Thinkpad4by3/chibitron/deflection_amp_5/deflection_amp_5/FOCUS_AMP.asc

C1: Cap; 100p
C2: Cap; 100p
Q1: npn
R1: Res; R=table(time,0,1000Meg,200ms,1000Meg,200.001ms,10Meg, 700ms,10Meg, 700.001ms, 1000Meg)
R2: Res; 5k
R3: Res; 5Meg
R4: Res; 10k
R5: Res; 100k
R6: Res; 100k
R12: Res; 3Meg
U2: LT1800
V1: Voltage; 10
V2: Voltage; PULSE(0 2 1p 40ms 40ms 20ms 0 10)
V4: Voltage; 2000
Named nets: 0, 5v, vout
.tran 1s
