Thinkpad4by3/chibitron/deflection_amp_5/deflection_amp_5/deflection_amp_3.kicad_sch

## KiCad design deflection_amp_5/deflection_amp_5/deflection_amp_3.kicad_sch (2026-02-02)

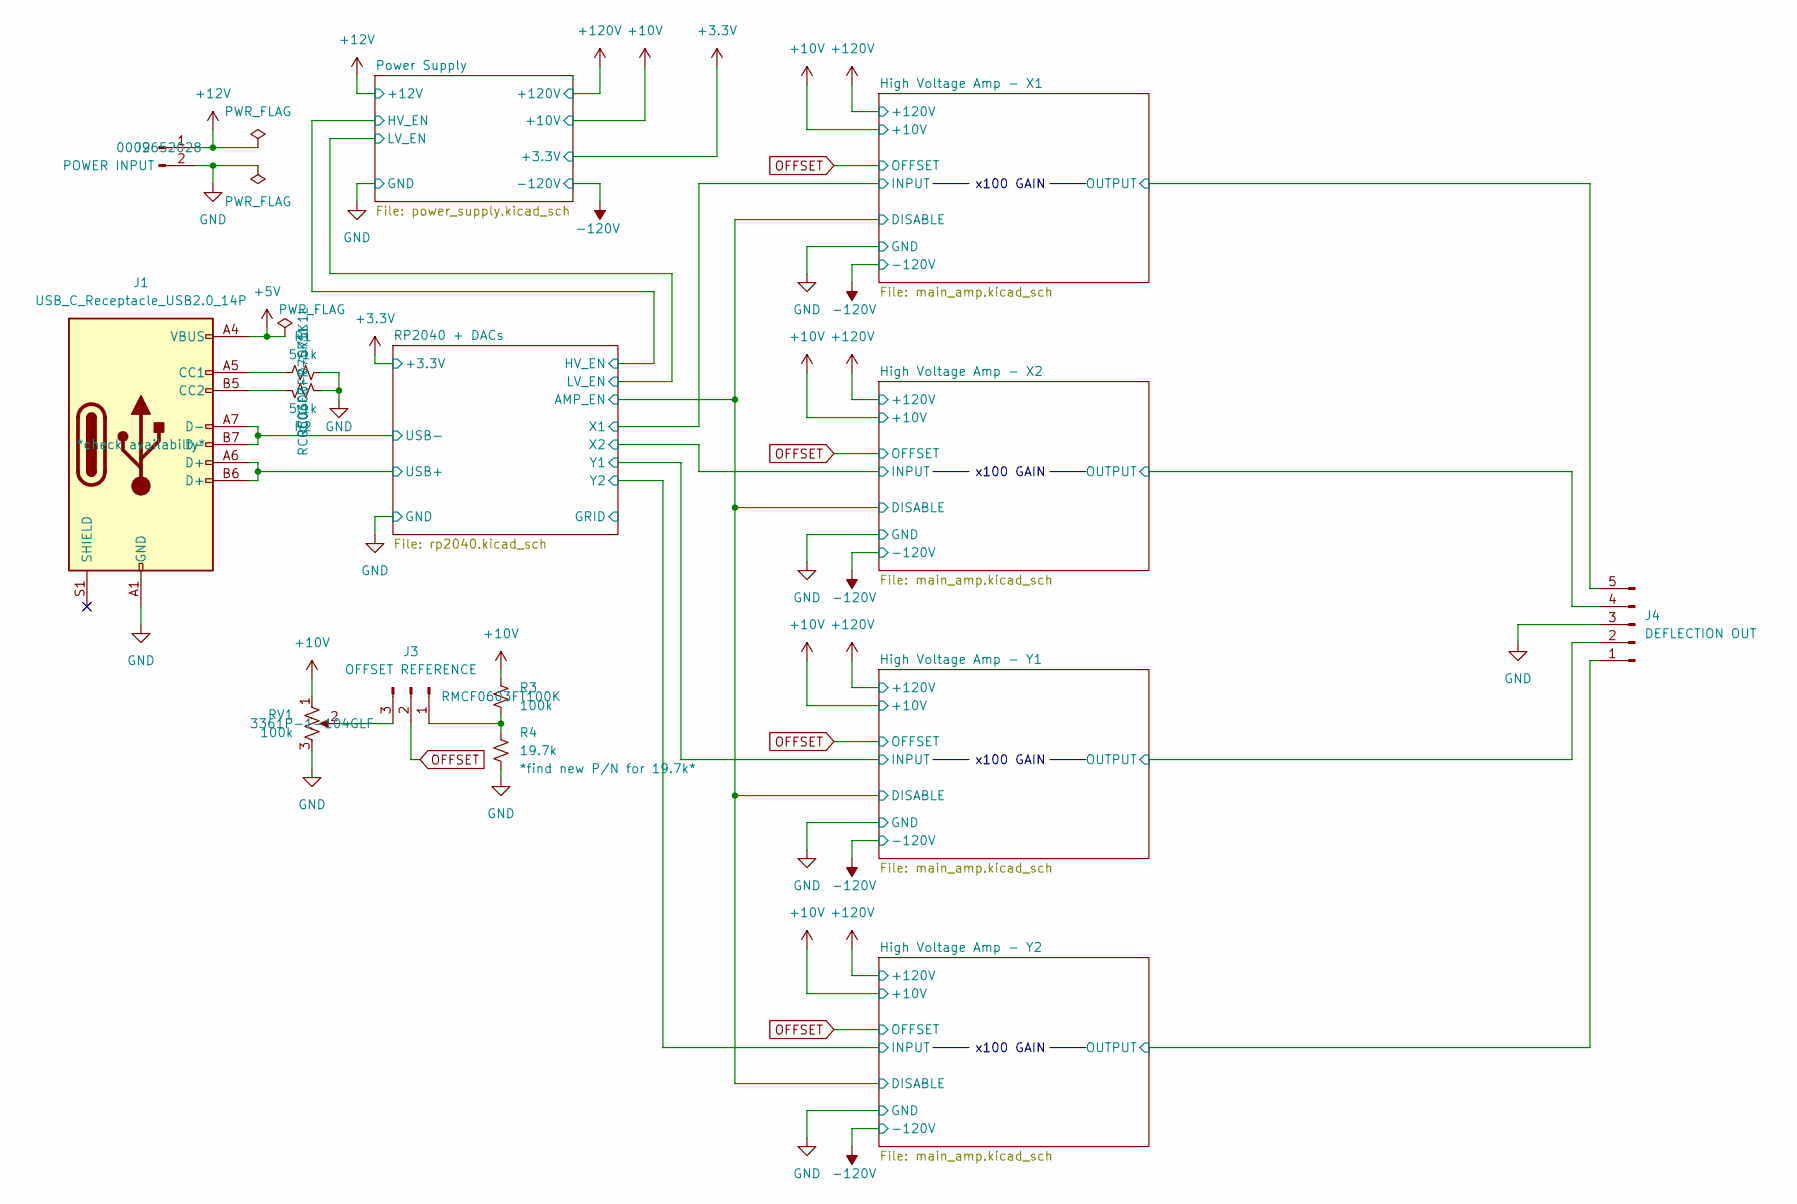
[picture p9: schematic deflection_amp_3.kicad_sch]

Parts:
J1: USB_C_Receptacle_USB2.0_14P; USB_C_Receptacle_HRO_TYPE-C-31-M-17; Digikey P/N *check availabilty*
J2: POWER INPUT; Molex_KK-396_5273-02A_1x02_P3.96mm_Vertical; Digikey P/N 0009652028
J3: OFFSET REFERENCE; PinSocket_1x03_P2.54mm_Vertical
J4: DEFLECTION OUT; Molex_KK-396_5273-05A_1x05_P3.96mm_Vertical
R1, R2: 5.1k; R_0603_1608Metric; Digikey P/N RC0603FR-075K1L
R3: 100k; R_0603_1608Metric; Digikey P/N RMCF0603FT100K
R4: 19.7k; R_0603_1608Metric; Digikey P/N *find new P/N for 19.7k*
RV1: 100k; Potentiometer_Vishay_TS53YJ_Vertical; Digikey P/N 3361P-1-104GLF

Connections:
+5V: J1.A4 (VBUS), J1.A9 (VBUS), J1.B4 (VBUS), J1.B9 (VBUS)
+10V: R3.1, RV1.1
+12V: J2.1
GND: J1.A1 (GND), J1.A12 (GND), J1.B1 (GND), J1.B12 (GND), J2.2, J4.3, R1.2, R2.2, R4.2, RV1.3
unnamed: J1.A5 (CC1), R1.1
unnamed: J1.B5 (CC2), R2.1
unnamed: J3.1, R3.2, R4.1
unnamed: J3.3, RV1.2
OFFSET: J3.2
OUTPUT: J4.1, J4.2, J4.4, J4.5
USB+: J1.A6 (D+), J1.B6 (D+)
USB-: J1.A7 (D-), J1.B7 (D-)

Notes on the sheet:
x100 GAIN
