Thinkpad4by3/chibitron/deflection_amp_5/deflection_amp_5/deflection_amp_5.kicad_sch

## KiCad design deflection_amp_5/deflection_amp_5/deflection_amp_5.kicad_sch (2026-02-02)

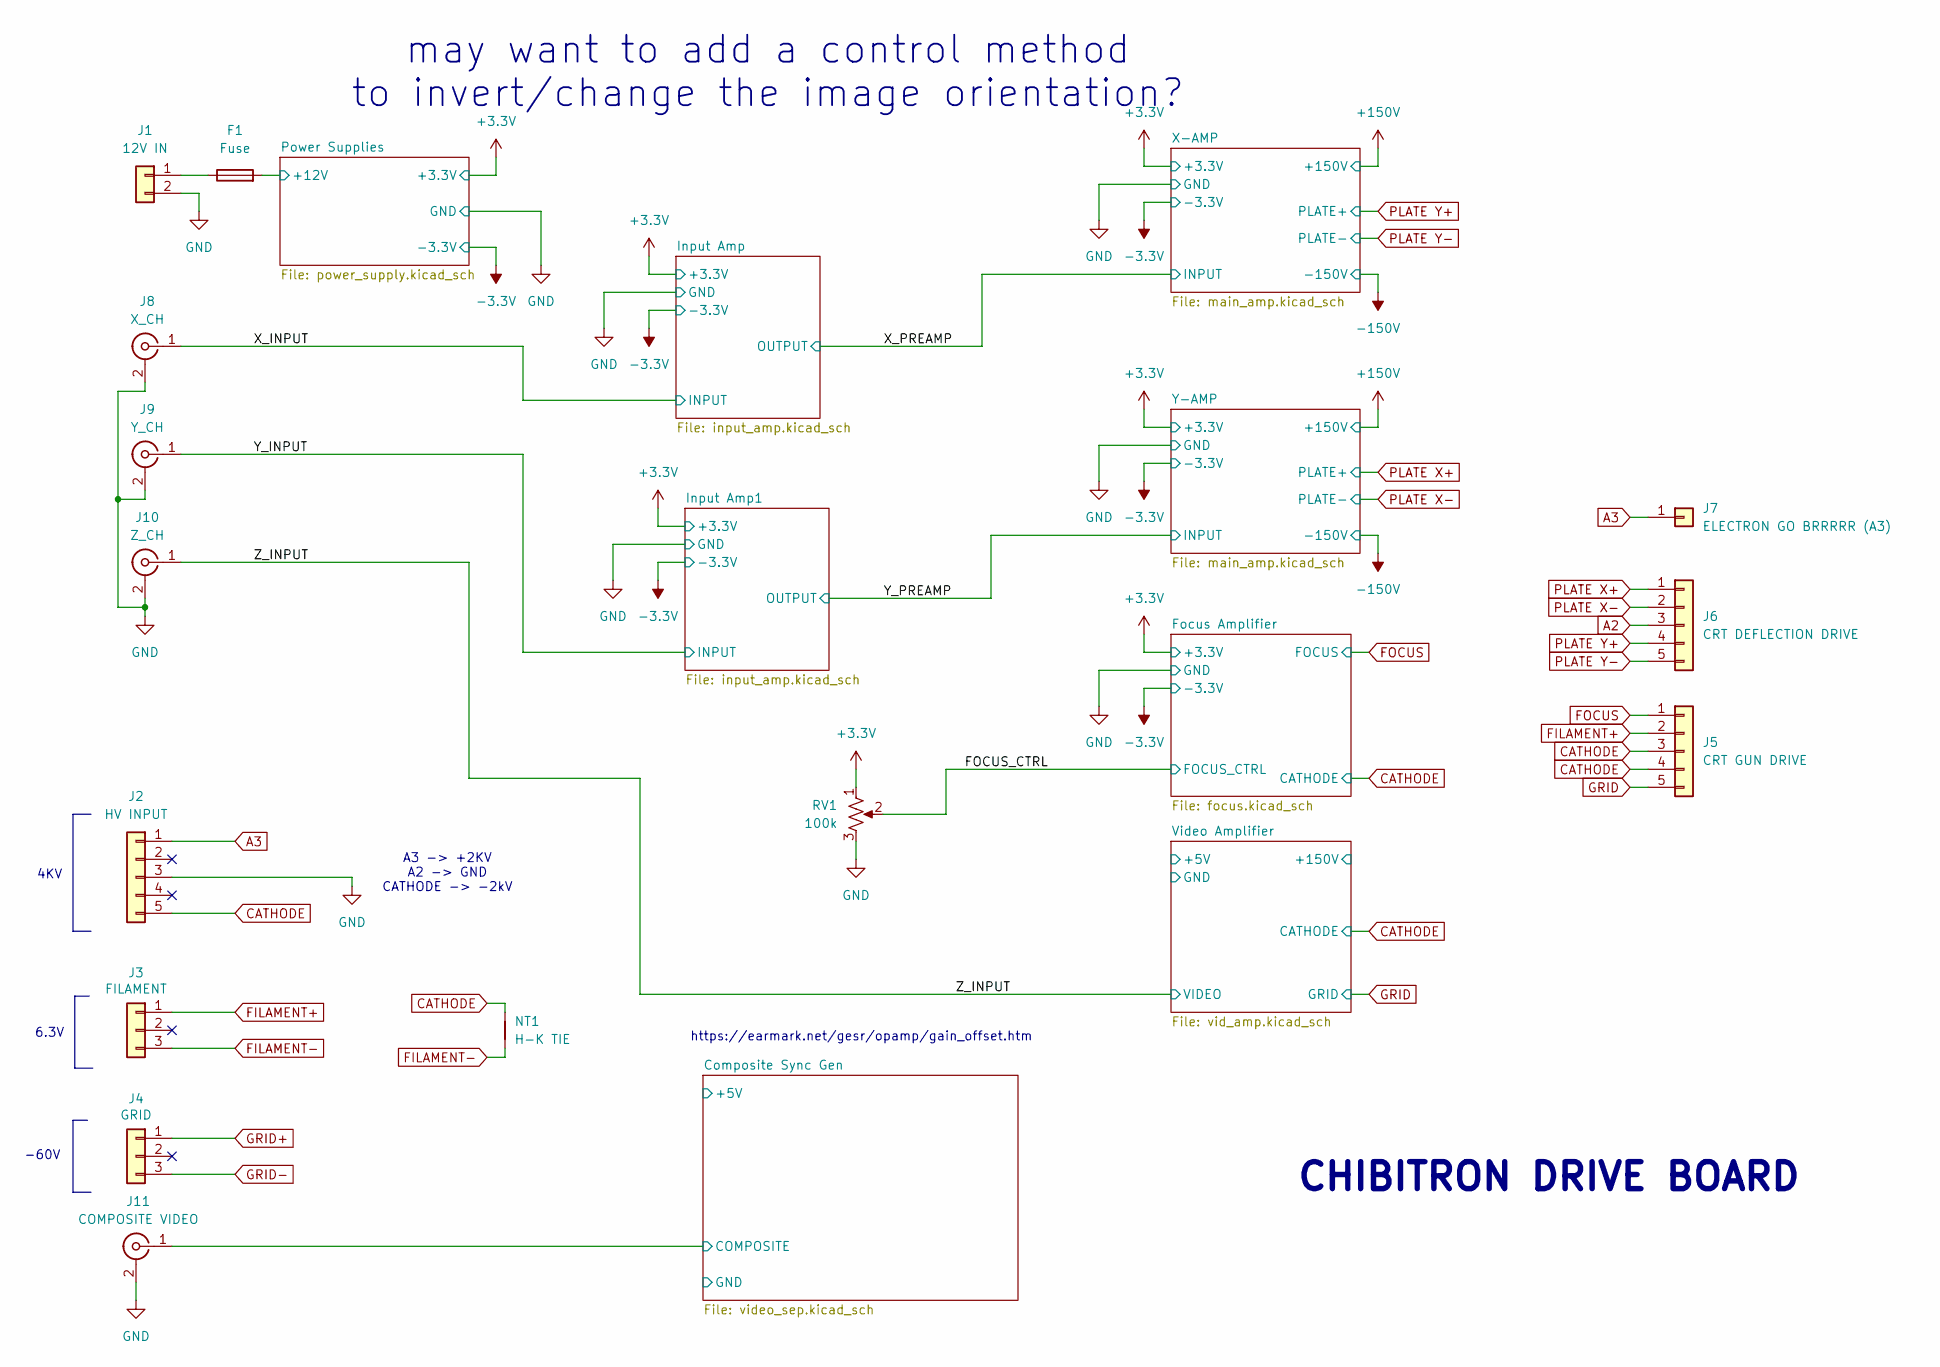
[picture p10: schematic deflection_amp_5.kicad_sch]

Parts:
F1: Fuse
J1: 12V IN
J2: HV INPUT
J3: FILAMENT
J4: GRID
J5: CRT GUN DRIVE
J6: CRT DEFLECTION DRIVE
J7: ELECTRON GO BRRRRR (A3)
J8: X_CH
J9: Y_CH
J10: Z_CH
J11: COMPOSITE VIDEO
NT1: H-K TIE
RV1: 100k

Connections:
+3.3V: RV1.1
+12V: F1.2
A2: J6.3
A3: J2.1, J7.1
CATHODE: J2.5, J5.3, J5.4, NT1.2
COMPOSITE: J11.1 (In)
FILAMENT+: J3.1, J5.2
FILAMENT-: J3.3, NT1.1
FOCUS: J5.1
FOCUS_CTRL: RV1.2
GND: J1.2, J2.3, J8.2 (Ext), J9.2 (Ext), J10.2 (Ext), J11.2 (Ext), RV1.3
GRID: J5.5
GRID+: J4.1
GRID-: J4.3
unnamed: F1.1, J1.1
PLATE X+: J6.1
PLATE X-: J6.2
PLATE Y+: J6.4
PLATE Y-: J6.5
X_INPUT: J8.1 (In)
Y_INPUT: J9.1 (In)
Z_INPUT: J10.1 (In)

Notes on the sheet:
A3 -> +2KV A2 -> GND CATHODE -> -2kV
CHIBITRON DRIVE BOARD
4KV
6.3V
https://earmark.net/gesr/opamp/gain_offset.htm
may want to add a control method to invert/change the image orientation?
-60V
