Thinkpad4by3/chibitron/deflection_amp_5/deflection_amp_5/focus.kicad_sch

## KiCad design deflection_amp_5/deflection_amp_5/focus.kicad_sch (2026-02-02)

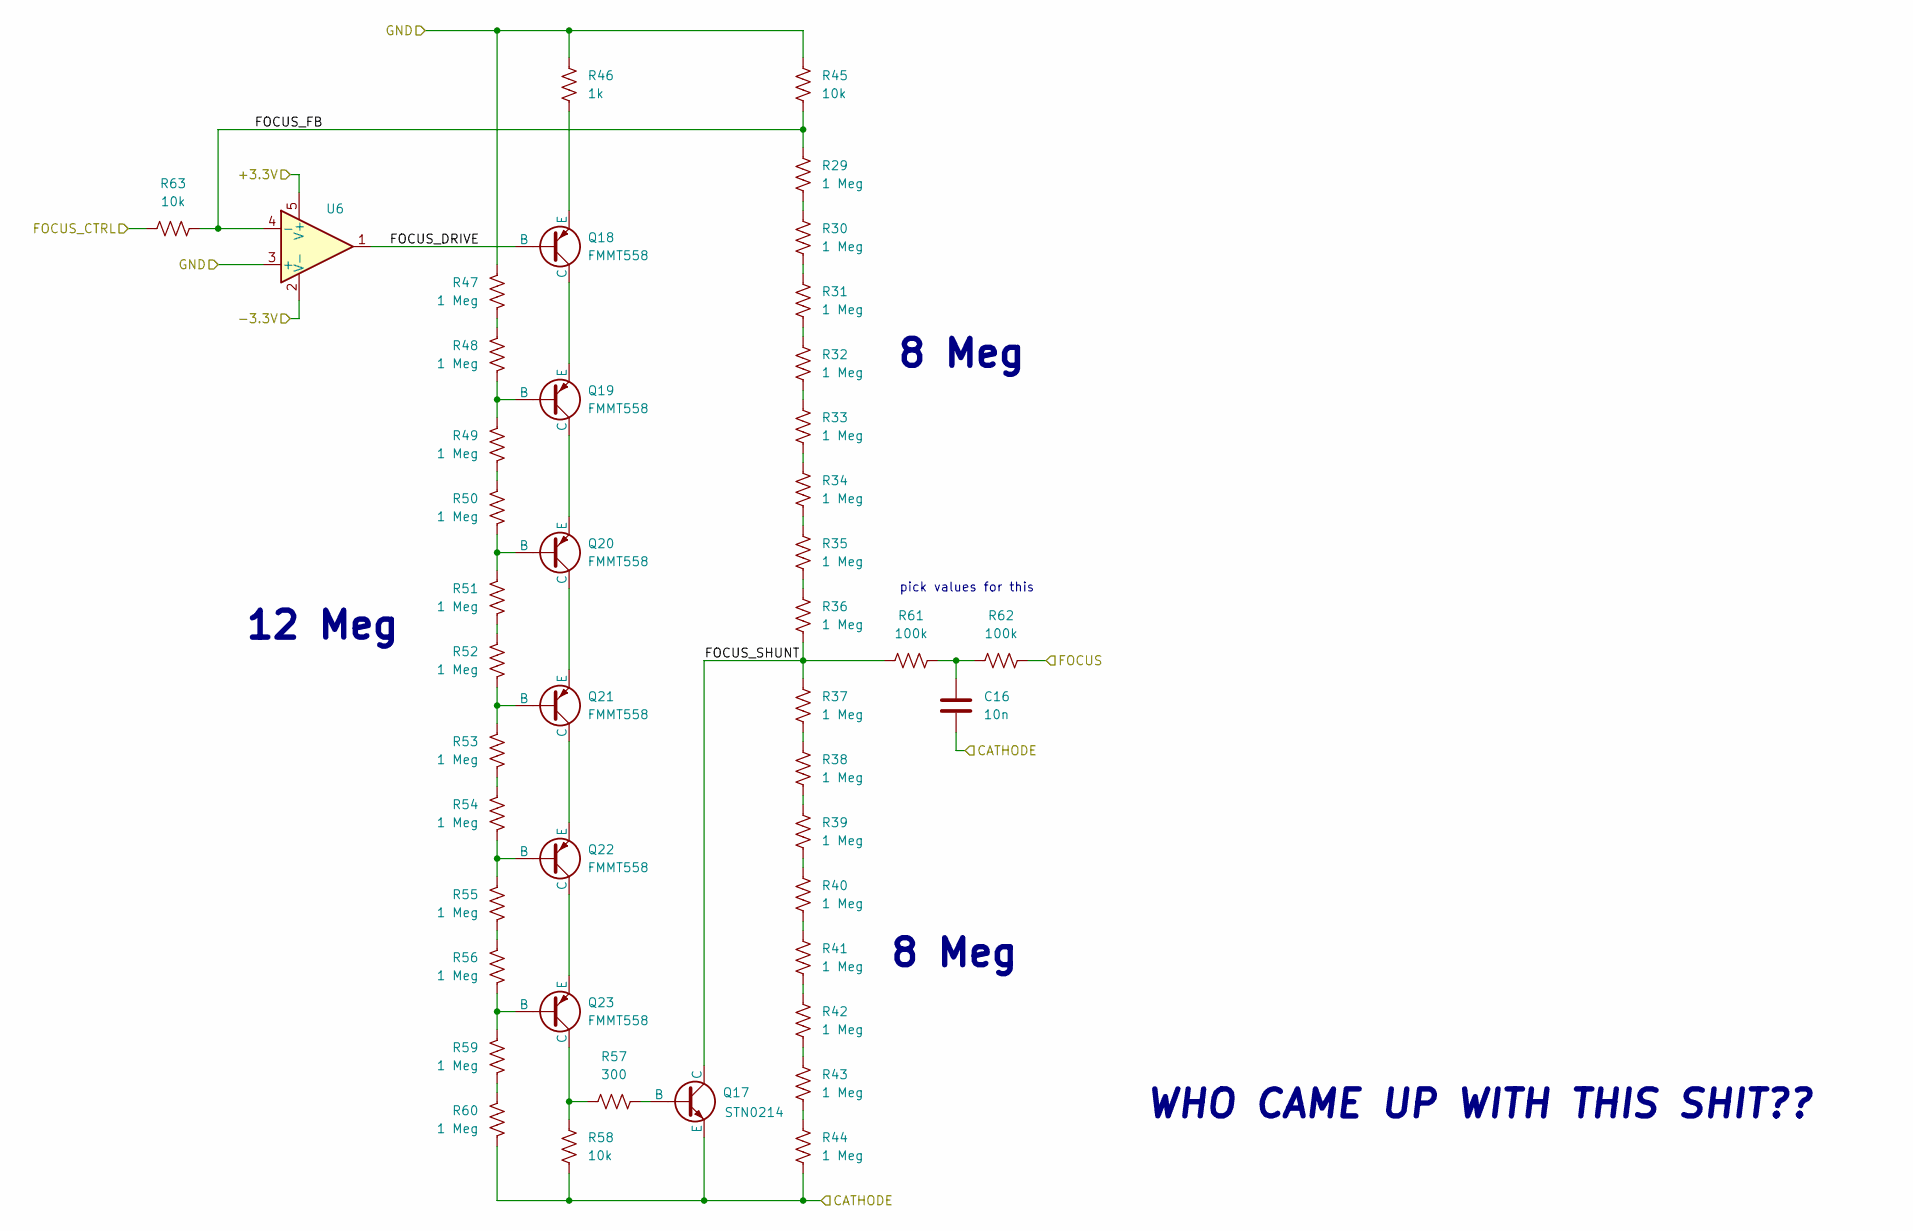
[picture p11: schematic focus.kicad_sch]

Parts:
C16: 10n
Q17: STN0214
Q18, Q19, Q20, Q21, Q22, Q23: FMMT558
R29, R30, R31, R32, R33, R34, R35, R36, R37, R38, R39, R40, R41, R42, R43, R44, R47, R48, R49, R50, R51, R52, R53, R54, R55, R56, R59, R60: 1 Meg; R_1206_3216Metric
R45, R58, R63: 10k
R46: 1k
R57: 300
R61, R62: 100k
U6: TLV2371DBV; SOT-23-5

Connections:
+3.3V: U6.5 (V+)
-3.3V: U6.2 (V-)
CATHODE: C16.2, Q17.3 (E), R44.2, R58.2, R60.2
FOCUS: R62.2
FOCUS_CTRL: R63.1
FOCUS_DRIVE: Q18.2 (B), U6.1
FOCUS_FB: R29.1, R45.2, R63.2, U6.4 (-)
FOCUS_SHUNT: Q17.1 (C), R36.2, R37.1, R61.1
GND: R45.1, R46.1, R47.1, U6.3 (+)
unnamed: C16.1, R61.2, R62.1
unnamed: Q17.2 (B), R57.2
unnamed: Q18.1 (C), Q19.3 (E)
unnamed: Q18.3 (E), R46.2
unnamed: Q19.1 (C), Q20.3 (E)
unnamed: Q19.2 (B), R48.2, R49.1
unnamed: Q20.1 (C), Q21.3 (E)
unnamed: Q20.2 (B), R50.2, R51.1
unnamed: Q21.1 (C), Q22.3 (E)
unnamed: Q21.2 (B), R52.2, R53.1
unnamed: Q22.1 (C), Q23.3 (E)
unnamed: Q22.2 (B), R54.2, R55.1
unnamed: Q23.1 (C), R57.1, R58.1
unnamed: Q23.2 (B), R56.2, R59.1
unnamed: R29.2, R30.1
unnamed: R30.2, R31.1
unnamed: R31.2, R32.1
unnamed: R32.2, R33.1
unnamed: R33.2, R34.1
unnamed: R34.2, R35.1
unnamed: R35.2, R36.1
unnamed: R37.2, R38.1
unnamed: R38.2, R39.1
unnamed: R39.2, R40.1
unnamed: R40.2, R41.1
unnamed: R41.2, R42.1
unnamed: R42.2, R43.1
unnamed: R43.2, R44.1
unnamed: R47.2, R48.1
unnamed: R49.2, R50.1
unnamed: R51.2, R52.1
unnamed: R53.2, R54.1
unnamed: R55.2, R56.1
unnamed: R59.2, R60.1

Notes on the sheet:
12 Meg
pick values for this
WHO CAME UP WITH THIS SHIT??
8 Meg
