Thinkpad4by3/chibitron/deflection_amp_5/deflection_amp_5/main_amp.kicad_sch

## KiCad design deflection_amp_5/deflection_amp_5/main_amp.kicad_sch (2026-02-02)

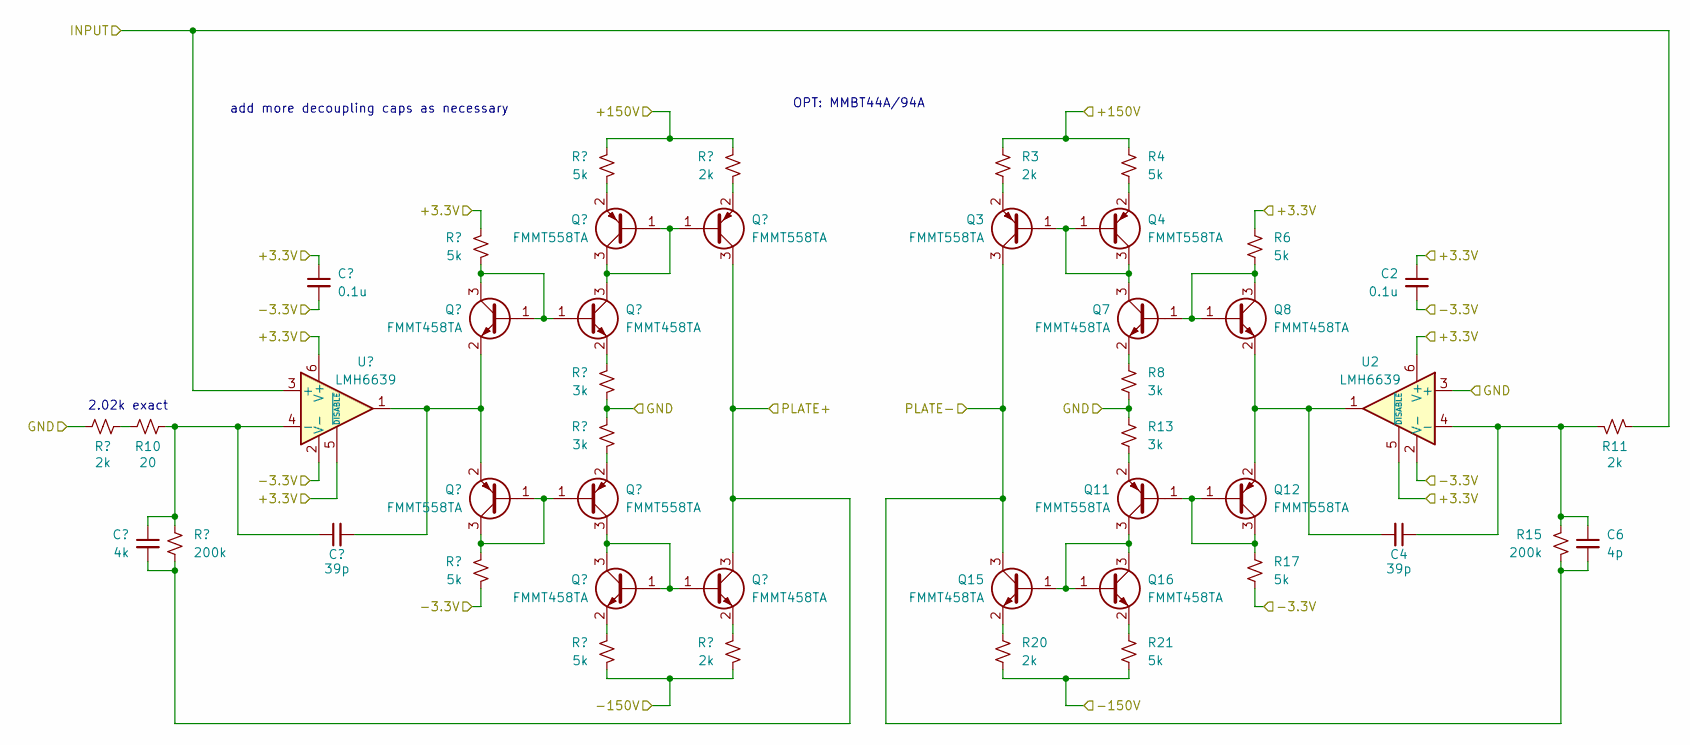
[picture p12: schematic main_amp.kicad_sch]

Parts:
C2, C18: 0.1u; C_0603_1608Metric; Digikey P/N C0603C104K5RAC7411
C4, C19: 39p; C_0603_1608Metric; Digikey P/N QSCP251Q390G1GV001T
C6: 4p; C_0603_1608Metric; Digikey P/N QSCP251Q2R0B1GV001T
C17: 4k; C_0603_1608Metric; Digikey P/N QSCP251Q2R0B1GV001T
Q3, Q4, Q11, Q12, Q25, Q27, Q28, Q30: FMMT558TA; SOT-23; Digikey P/N FMMT558TA
Q7, Q8, Q15, Q16, Q24, Q26, Q29, Q31: FMMT458TA; SOT-23; Digikey P/N FMMT458TA
R3, R11, R20, R64, R73, R74: 2k; R_1206_3216Metric; Digikey P/N RMCF1206FT2K00
R4, R21, R69, R72: 5k; R_1206_3216Metric; Digikey P/N RT1206FRE075KL
R6, R17, R67, R68: 5k; R_0603_1608Metric; Digikey P/N RC0603FR-0710KL
R8, R13, R70, R71: 3k; R_1206_3216Metric; Digikey P/N RMCF1206FT2K00
R10: 20; R_1206_3216Metric; Digikey P/N RMCF1206FT2K00
R15, R66: 200k; R_1206_3216Metric; Digikey P/N RC1206JR-07200KL
U2, U7: LMH6639; TSOT-23-6; Digikey P/N LMH6639MFX/NOPB

Connections:
+3.3V: C2.1, C18.1, R6.1, R67.1, U2.5 (~DISABLE), U2.6 (V+), U7.5 (~DISABLE), U7.6 (V+)
+150V: R3.1, R4.1, R69.1, R73.1
-3.3V: C2.2, C18.2, R17.2, R68.2, U2.2 (V-), U7.2 (V-)
-150V: R20.2, R21.2, R72.2, R74.2
GND: R8.2, R13.1, R64.2, R70.2, R71.1, U2.3 (+)
INPUT: R11.2, U7.3 (+)
unnamed: C4.1, C6.1, R11.1, R15.1, U2.4 (-)
unnamed: C4.2, Q8.2 (E), Q12.2 (E), U2.1
unnamed: C17.1, C19.1, R10.1, R66.1, U7.4 (-)
unnamed: C19.2, Q24.2 (E), Q25.2 (E), U7.1
unnamed: Q3.1 (B), Q4.1 (B), Q4.3 (C), Q7.3 (C)
unnamed: Q3.2 (E), R3.2
unnamed: Q4.2 (E), R4.2
unnamed: Q7.1 (B), Q8.1 (B), Q8.3 (C), R6.2
unnamed: Q7.2 (E), R8.1
unnamed: Q11.1 (B), Q12.1 (B), Q12.3 (C), R17.1
unnamed: Q11.2 (E), R13.2
unnamed: Q11.3 (C), Q15.1 (B), Q16.1 (B), Q16.3 (C)
unnamed: Q15.2 (E), R20.1
unnamed: Q16.2 (E), R21.1
unnamed: Q24.1 (B), Q24.3 (C), Q26.1 (B), R67.2
unnamed: Q25.1 (B), Q25.3 (C), Q27.1 (B), R68.1
unnamed: Q26.2 (E), R70.1
unnamed: Q26.3 (C), Q28.1 (B), Q28.3 (C), Q30.1 (B)
unnamed: Q27.2 (E), R71.2
unnamed: Q27.3 (C), Q29.1 (B), Q29.3 (C), Q31.1 (B)
unnamed: Q28.2 (E), R69.2
unnamed: Q29.2 (E), R72.1
unnamed: Q30.2 (E), R73.2
unnamed: Q31.2 (E), R74.1
unnamed: R10.2, R64.1
PLATE+: C17.2, Q30.3 (C), Q31.3 (C), R66.2
PLATE-: C6.2, Q3.3 (C), Q15.3 (C), R15.2

Notes on the sheet:
2.02k exact
add more decoupling caps as necessary
OPT: MMBT44A/94A
