Thinkpad4by3/chibitron/deflection_amp_5/deflection_amp_5/power_supply.kicad_sch

## KiCad design deflection_amp_5/deflection_amp_5/power_supply.kicad_sch (2026-02-02)

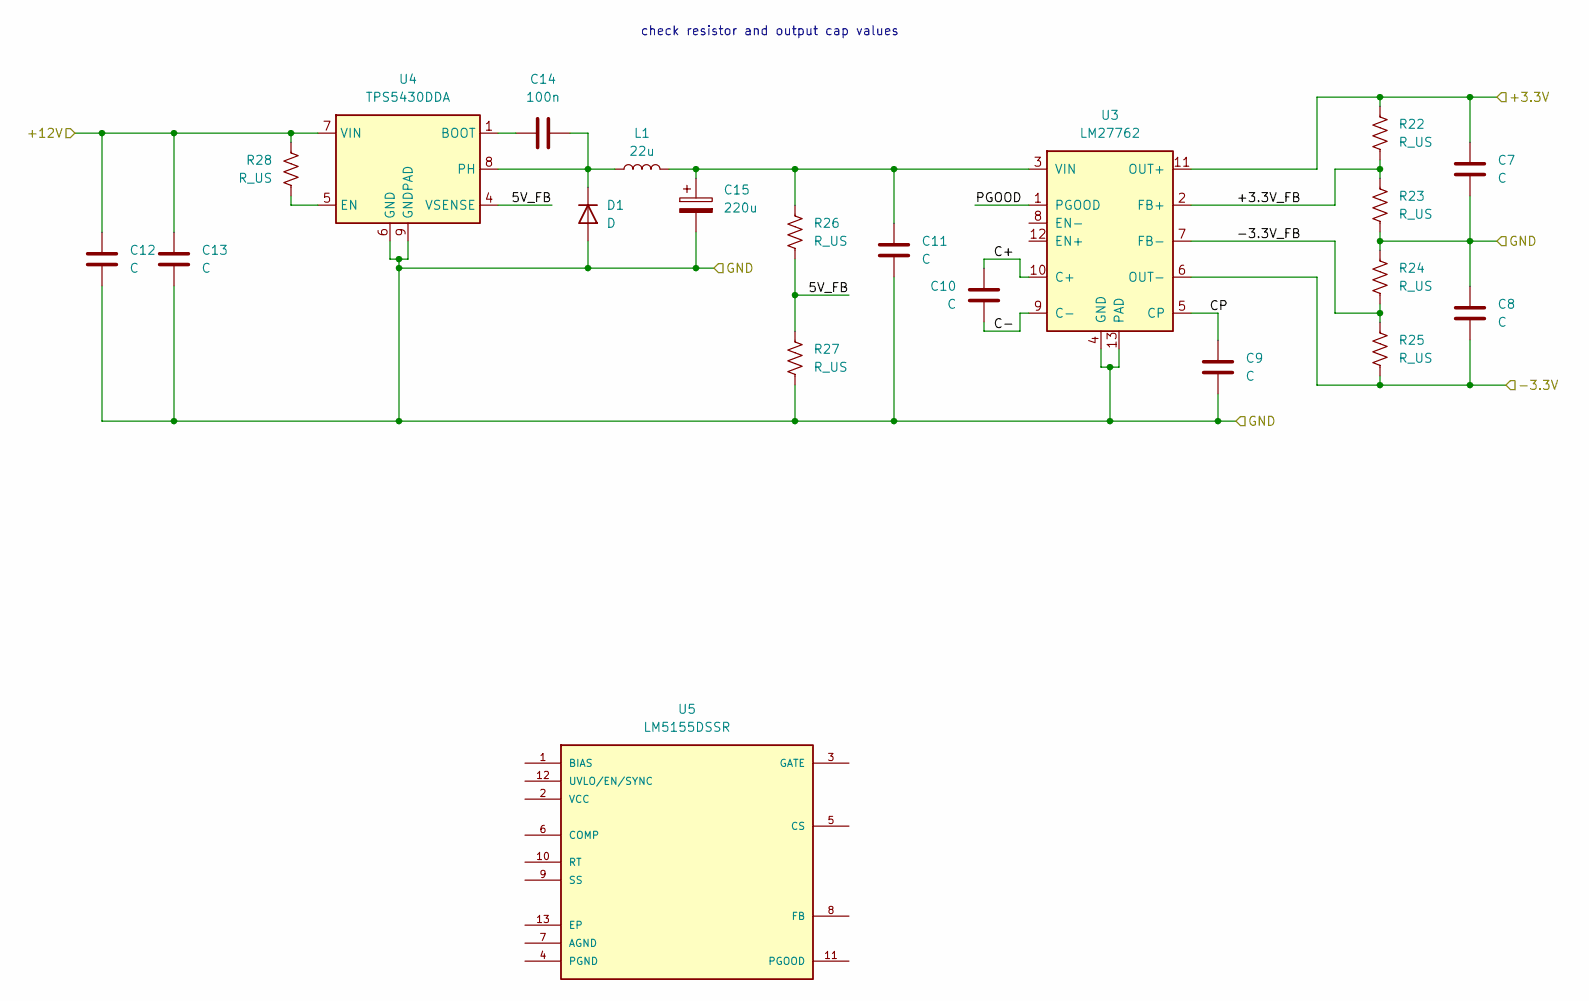
[picture p13: schematic power_supply.kicad_sch]

Parts:
C7, C8, C9, C10, C11, C12, C13: C
C14: 100n
C15: 220u
D1: D
L1: 22u
R22, R23, R24, R25, R26, R27, R28: R_US
U3: LM27762; WSON-12-1EP_3x2mm_P0.5mm_EP1x2.65_ThermalVias
U4: TPS5430DDA; TI_SO-PowerPAD-8_ThermalVias
U5: LM5155DSSR; IC_LM5155DSSR; PARTREV E

Connections:
5V_FB: R26.2, R27.1, U4.4 (VSENSE)
+3.3V: C7.1, R22.1, U3.11 (OUT+)
+3.3V_FB: R22.2, R23.1, U3.2 (FB+)
+12V: C12.1, C13.1, R28.1, U4.7 (VIN)
-3.3V: C8.2, R25.2, U3.6 (OUT-)
-3.3V_FB: R24.2, R25.1, U3.7 (FB-)
C+: C10.1, U3.10 (C+)
C-: C10.2, U3.9 (C-)
CP: C9.1, U3.5 (CP)
GND: C7.2, C8.1, C9.2, C11.2, C12.2, C13.2, C15.2, D1.2 (A), R23.2, R24.1, R27.2, U3.4 (GND), U3.13 (PAD), U4.6 (GND), U4.9 (GNDPAD)
unnamed: C11.1, C15.1, L1.2, R26.1, U3.3 (VIN)
unnamed: C14.1, U4.1 (BOOT)
unnamed: C14.2, D1.1 (K), L1.1, U4.8 (PH)
unnamed: R28.2, U4.5 (EN)
PGOOD: U3.1 (PGOOD)

Notes on the sheet:
check resistor and output cap values
