Thinkpad4by3/chibitron/deflection_amp_5/deflection_amp_5/rp2040.kicad_sch

## KiCad design deflection_amp_5/deflection_amp_5/rp2040.kicad_sch (2026-02-02)

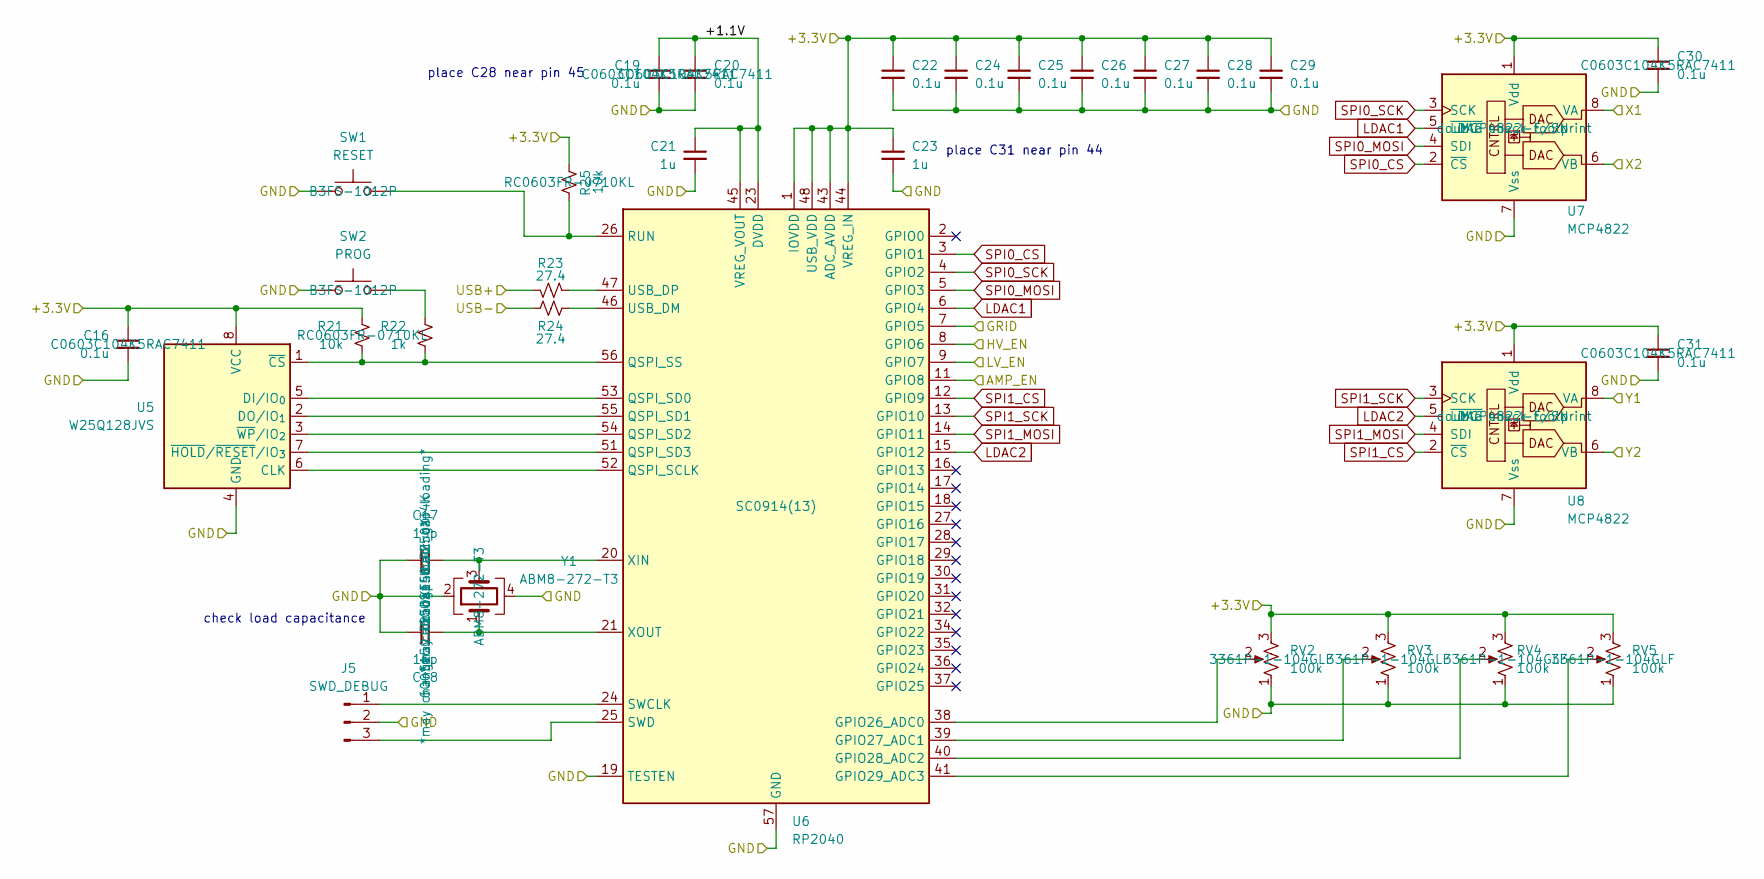
[picture p14: schematic rp2040.kicad_sch]

Parts:
C16, C19, C20, C22, C24, C25, C26, C27, C28, C29, C30, C31: 0.1u; C_0603_1608Metric; Digikey P/N C0603C104K5RAC7411
C17, C18: 15p; C_0603_1608Metric; Digikey P/N 600S150JT250XT4K
C21, C23: 1u; C_0603_1608Metric; Digikey P/N CL10A105KA8NNNC
J5: SWD_DEBUG; PinHeader_1x03_P2.54mm_Vertical
R21, R25: 10k; R_0603_1608Metric; Digikey P/N RC0603FR-0710KL
R22: 1k
R23, R24: 27.4
RV2, RV3, RV4, RV5: 100k; Potentiometer_Vishay_TS53YJ_Vertical; Digikey P/N 3361P-1-104GLF
SW1: RESET; SW_SPST_Omron_B3FS-101xP; Digikey P/N B3FS-1012P
SW2: PROG; SW_SPST_Omron_B3FS-101xP; Digikey P/N B3FS-1012P
U5: W25Q128JVS; SOIC-8_5.3x5.3mm_P1.27mm
U6: RP2040; QFN-56-1EP_7x7mm_P0.4mm_EP3.2x3.2mm; Digikey P/N SC0914(13)
U7, U8: MCP4822; SOIC-8_5.3x5.3mm_P1.27mm; Digikey P/N MCP4822-E/SN
Y1: ABM8-272-T3; Crystal_SMD_3225-4Pin_3.2x2.5mm; Digikey P/N ABM8-272-T3

Connections:
+1.1V: C19.1, C20.1, C21.1, U6.23 (DVDD), U6.45 (VREG_VOUT), U6.50 (DVDD)
+3.3V: C16.1, C22.1, C23.1, C24.1, C25.1, C26.1, C27.1, C28.1, C29.1, C30.1, C31.1, R21.1, R25.2, RV2.3, RV3.3, RV4.3, RV5.3, U5.8 (VCC), U6.1 (IOVDD), U6.10 (IOVDD), U6.22 (IOVDD), U6.33 (IOVDD), U6.42 (IOVDD), U6.43 (ADC_AVDD), U6.44 (VREG_IN), U6.48 (USB_VDD), U6.49 (IOVDD), U7.1 (Vdd), U8.1 (Vdd)
AMP_EN: U6.11 (GPIO8)
GND: C16.2, C17.1, C18.1, C19.2, C20.2, C21.2, C22.2, C23.2, C24.2, C25.2, C26.2, C27.2, C28.2, C29.2, C30.2, C31.2, J5.2, RV2.1, RV3.1, RV4.1, RV5.1, SW1.1, SW2.1, U5.4 (GND), U6.19 (TESTEN), U6.57 (GND), U7.7 (Vss), U8.7 (Vss), Y1.2, Y1.4
GRID: U6.7 (GPIO5)
HV_EN: U6.8 (GPIO6)
LDAC1: U6.6 (GPIO4), U7.5 (~LDAC)
LDAC2: U6.15 (GPIO12), U8.5 (~LDAC)
LV_EN: U6.9 (GPIO7)
unnamed: C17.2, U6.20 (XIN), Y1.3
unnamed: C18.2, U6.21 (XOUT), Y1.1
unnamed: J5.1, U6.24 (SWCLK)
unnamed: J5.3, U6.25 (SWD)
unnamed: R21.2, R22.2, U5.1 (~CS), U6.56 (QSPI_SS)
unnamed: R22.1, SW2.2
unnamed: R23.2, U6.47 (USB_DP)
unnamed: R24.2, U6.46 (USB_DM)
unnamed: R25.1, SW1.2, U6.26 (RUN)
unnamed: RV2.2, U6.38 (GPIO26_ADC0)
unnamed: RV3.2, U6.39 (GPIO27_ADC1)
unnamed: RV4.2, U6.40 (GPIO28_ADC2)
unnamed: RV5.2, U6.41 (GPIO29_ADC3)
unnamed: U5.2 (DO/IO_{1}), U6.55 (QSPI_SD1)
unnamed: U5.3 (~WP/IO_{2}), U6.54 (QSPI_SD2)
unnamed: U5.5 (DI/IO_{0}), U6.53 (QSPI_SD0)
unnamed: U5.6 (CLK), U6.52 (QSPI_SCLK)
unnamed: U5.7 (~HOLD/~RESET/IO_{3}), U6.51 (QSPI_SD3)
SPI0_CS: U6.3 (GPIO1), U7.2 (~CS)
SPI0_MOSI: U6.5 (GPIO3), U7.4 (SDI)
SPI0_SCK: U6.4 (GPIO2), U7.3 (SCK)
SPI1_CS: U6.12 (GPIO9), U8.2 (~CS)
SPI1_MOSI: U6.14 (GPIO11), U8.4 (SDI)
SPI1_SCK: U6.13 (GPIO10), U8.3 (SCK)
USB+: R23.1
USB-: R24.1
X1: U7.8 (VA)
X2: U7.6 (VB)
Y1: U8.8 (VA)
Y2: U8.6 (VB)

Notes on the sheet:
place C28 near pin 45
place C31 near pin 44
check load capacitance
