Thinkpad4by3/chibitron/deflection_amp_5/deflection_amp_5/video_sep.kicad_sch

## KiCad design deflection_amp_5/deflection_amp_5/video_sep.kicad_sch (2026-02-02)

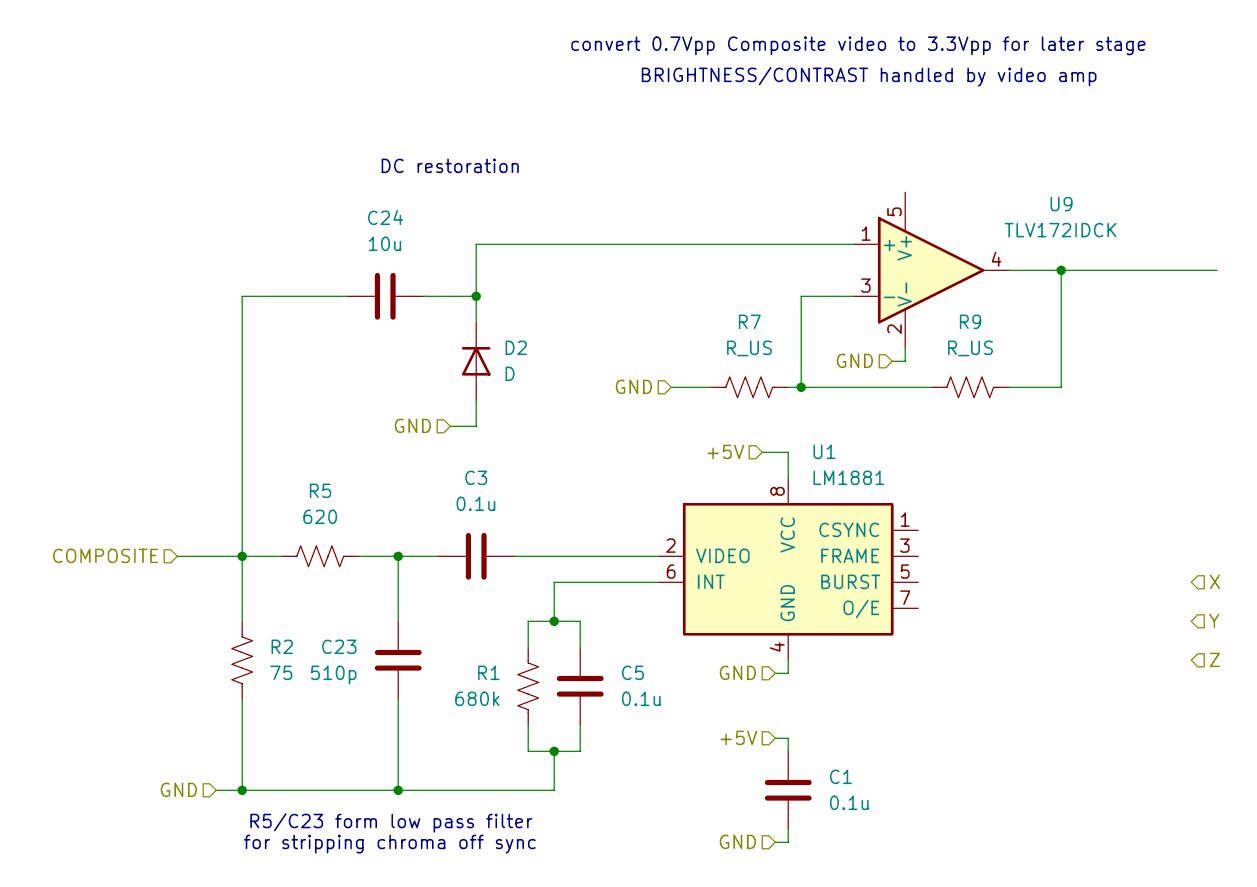
[picture p15: schematic video_sep.kicad_sch]

Parts:
C1, C3, C5: 0.1u
C23: 510p
C24: 10u
D2: D
R1: 680k
R2: 75
R5: 620
R7, R9: R_US
U1: LM1881
U9: TLV172IDCK; SOT-353_SC-70-5

Connections:
+5V: C1.1, U1.8 (VCC)
COMPOSITE: C24.1, R2.1, R5.1
GND: C1.2, C5.1, C23.2, D2.2 (A), R1.2, R2.2, R7.1, U1.4 (GND), U9.2 (V-)
unnamed: C3.2, U1.2 (VIDEO)
unnamed: C5.2, R1.1, U1.6 (INT)
unnamed: C3.1, C23.1, R5.2
unnamed: C24.2, D2.1 (K), U9.1 (+)
unnamed: R7.2, R9.1, U9.3 (-)
unnamed: R9.2, U9.4

Notes on the sheet:
BRIGHTNESS/CONTRAST handled by video amp
convert 0.7Vpp Composite video to 3.3Vpp for later stage
DC restoration
R5/C23 form low pass filter for stripping chroma off sync
